fm4dd/pmod2rpi/images/osc-symbol.bmp

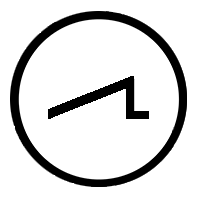
images/osc-symbol.bmp
