fm4dd/pmod2rpi/images/pmod2rpi-bottom-v10.png

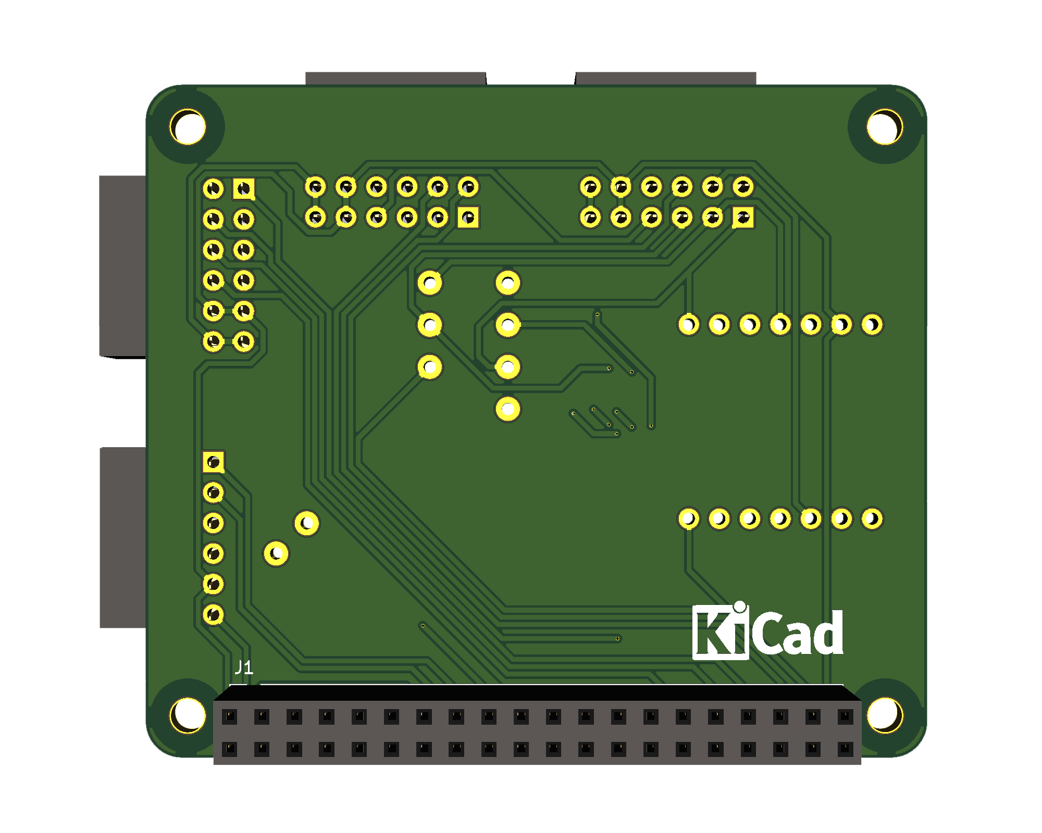
images/pmod2rpi-bottom-v10.png
