fm4dd/pmod2rpi/images/pmod2rpi-pcb-layout-v10.png

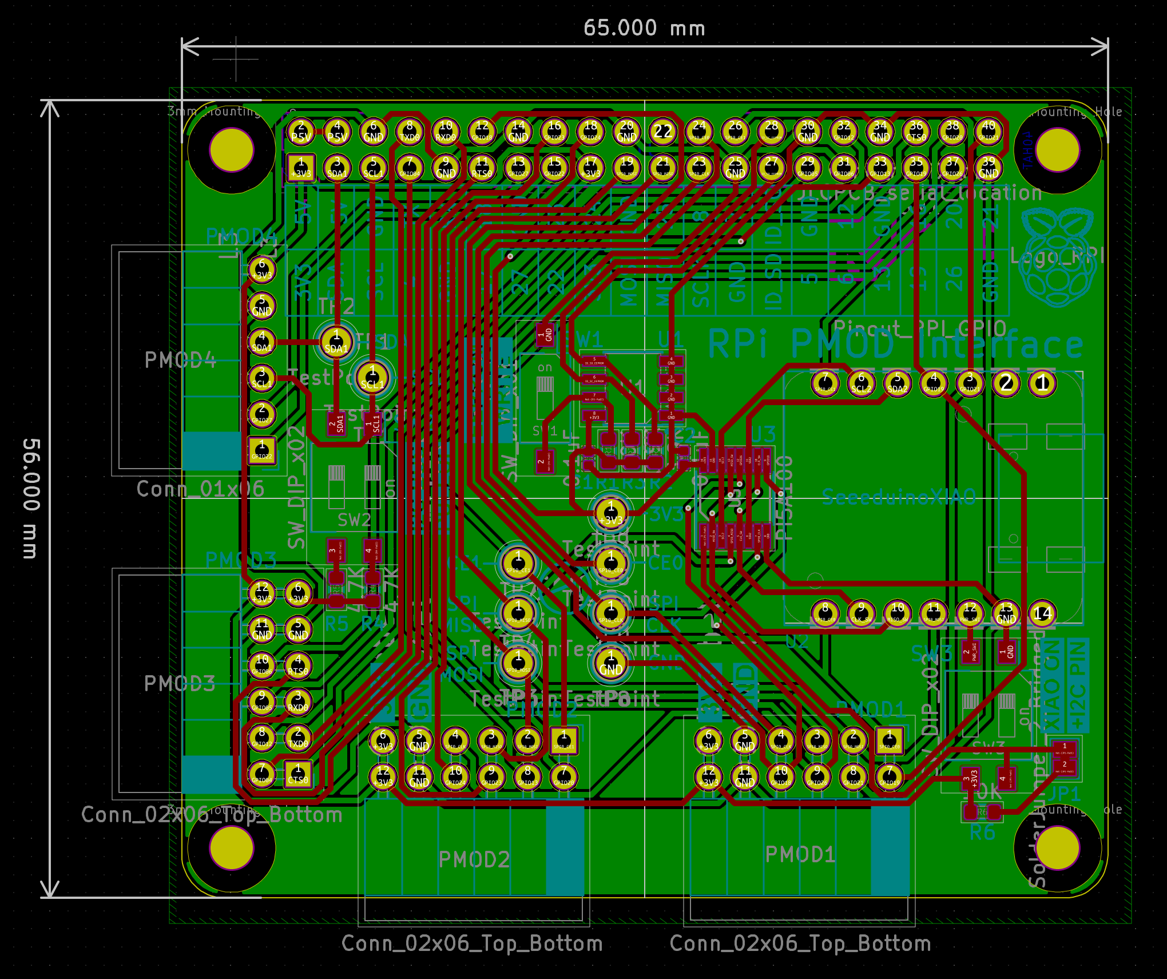
images/pmod2rpi-pcb-layout-v10.png
