fm4dd/pmod2rpi/images/pmod2rpi-xiao-8led-pmod1-v10.png

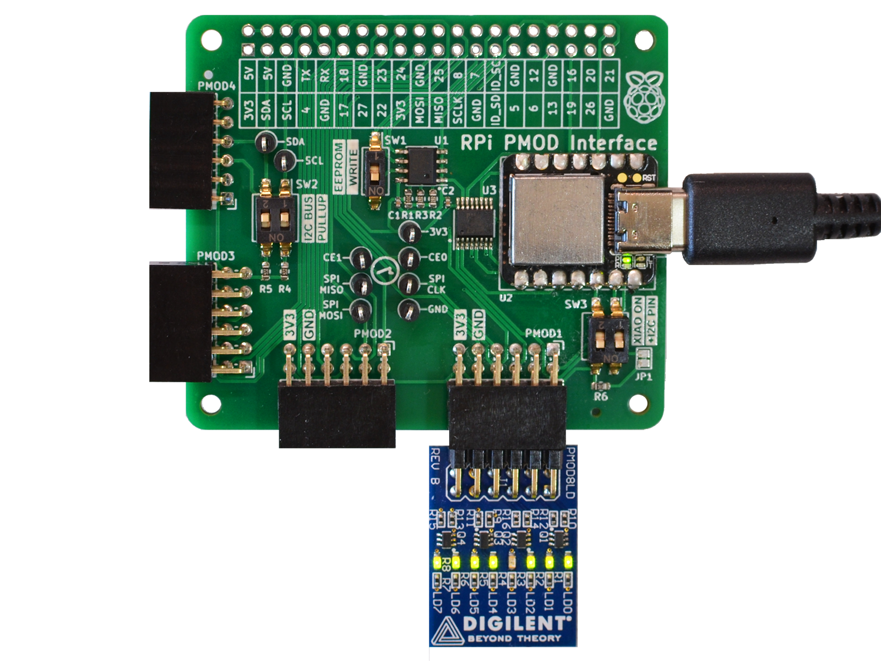
images/pmod2rpi-xiao-8led-pmod1-v10.png
