fm4dd/pmod2rpi/images/xiao-on.bmp

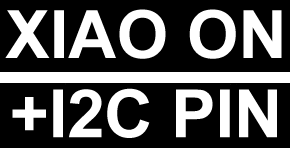
images/xiao-on.bmp
